utydfd/BikeNav/Arduino/BikeNav/page_speedometer.h

// page_speedometer.h
#ifndef PAGE_SPEEDOMETER_H
#define PAGE_SPEEDOMETER_H
#include <GxEPD2_BW.h>
#include <U8g2_for_Adafruit_GFX.h>
#include <TinyGPS++.h>
#include "notification_system.h"
#include "status_bar.h"

extern GxEPD2_BW<GxEPD2_290_BS, GxEPD2_290_BS::HEIGHT> display;
extern U8G2_FOR_ADAFRUIT_GFX u8g2_display;
extern const int DISPLAY_WIDTH;
extern const int DISPLAY_HEIGHT;
extern TinyGPSPlus gps;
extern bool gpsValid;
extern const unsigned char ICON_SPEEDOMETER[];

// Speedometer state
struct SpeedometerState {
  float currentSpeed;      // km/h
  float maxSpeed;          // km/h
  float averageSpeed;      // km/h (calculated from distance / time)
  float totalDistance;     // km
  unsigned long tripStartTime;
  unsigned long lastUpdateTime;
  bool tripActive;
  bool showGPSDialog;
  bool showResetDialog;
};

SpeedometerState speedoState = {
  0.0,                     // currentSpeed
  0.0,                     // maxSpeed
  0.0,                     // averageSpeed
  0.0,                     // totalDistance
  0,                       // tripStartTime
  0,                       // lastUpdateTime
  false,                   // tripActive
  false,                   // showGPSDialog
  false                    // showResetDialog
};

const int SPEEDOMETER_SPLIT_HEIGHT = 40;
bool speedometerSplitEnabled = false;

void initSpeedometerPage() {
  // Check if GPS is valid, if not show dialog
  if (!gpsValid) {
    speedoState.showGPSDialog = true;
  }

  // Start trip if GPS is valid
  if (gpsValid && !speedoState.tripActive) {
    speedoState.tripStartTime = millis();
    speedoState.lastUpdateTime = millis();
    speedoState.tripActive = true;
  }
}

void drawGPSDialog() {
  // Dialog dimensions - larger to fit text
  int dialogWidth = 110;
  int dialogHeight = 100;
  int dialogX = (DISPLAY_WIDTH - dialogWidth) / 2;
  int dialogY = (DISPLAY_HEIGHT - dialogHeight) / 2 - 20;

  // Draw shadow (offset by 2 pixels)
  display.fillRect(dialogX + 2, dialogY + 2, dialogWidth, dialogHeight, GxEPD_BLACK);

  // Draw dialog background
  display.fillRect(dialogX, dialogY, dialogWidth, dialogHeight, GxEPD_WHITE);
  display.drawRect(dialogX, dialogY, dialogWidth, dialogHeight, GxEPD_BLACK);
  display.drawRect(dialogX + 1, dialogY + 1, dialogWidth - 2, dialogHeight - 2, GxEPD_BLACK);

  // Setup text rendering
  u8g2_display.setFontMode(1);
  u8g2_display.setForegroundColor(GxEPD_BLACK);
  u8g2_display.setBackgroundColor(GxEPD_WHITE);

  // Title - use larger bold font and split into 2 lines
  u8g2_display.setFont(u8g2_font_helvB12_tf);
  const char* title1 = "GPS";
  const char* title2 = "Unavailable";
  int title1Width = u8g2_display.getUTF8Width(title1);
  int title2Width = u8g2_display.getUTF8Width(title2);
  u8g2_display.setCursor(dialogX + (dialogWidth - title1Width) / 2, dialogY + 16);
  u8g2_display.print(title1);
  u8g2_display.setCursor(dialogX + (dialogWidth - title2Width) / 2, dialogY + 30);
  u8g2_display.print(title2);

  // Message
  u8g2_display.setFont(u8g2_font_helvB08_tf);
  const char* msg1 = "No GPS signal";
  const char* msg2 = "detected";
  int msg1Width = u8g2_display.getUTF8Width(msg1);
  int msg2Width = u8g2_display.getUTF8Width(msg2);
  u8g2_display.setCursor(dialogX + (dialogWidth - msg1Width) / 2, dialogY + 50);
  u8g2_display.print(msg1);
  u8g2_display.setCursor(dialogX + (dialogWidth - msg2Width) / 2, dialogY + 62);
  u8g2_display.print(msg2);

  // OK button
  int buttonWidth = 40;
  int buttonHeight = 18;
  int buttonX = dialogX + (dialogWidth - buttonWidth) / 2;
  int buttonY = dialogY + dialogHeight - buttonHeight - 6;

  display.fillRect(buttonX, buttonY, buttonWidth, buttonHeight, GxEPD_BLACK);

  u8g2_display.setFont(u8g2_font_helvB10_tf);
  u8g2_display.setForegroundColor(GxEPD_WHITE);
  u8g2_display.setBackgroundColor(GxEPD_BLACK);
  const char* buttonText = "OK";
  int buttonTextWidth = u8g2_display.getUTF8Width(buttonText);
  u8g2_display.setCursor(buttonX + (buttonWidth - buttonTextWidth) / 2, buttonY + 13);
  u8g2_display.print(buttonText);
}
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
